andy5211d/SYMS17.0/pictures/IMG_2306.JPG

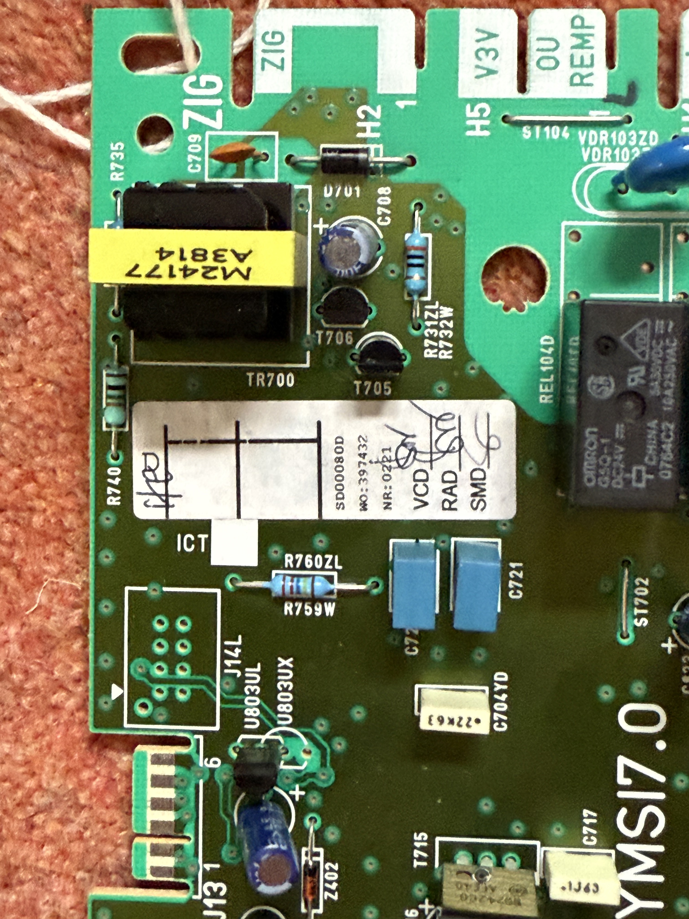
pictures/IMG_2306.JPG
