andy5211d/SYMS17.0/schematic/KiCad 8 Files/SYMS17.0.kicad_sch

## KiCad design schematic/KiCad 8 Files/SYMS17.0.kicad_sch (2025-01-01)

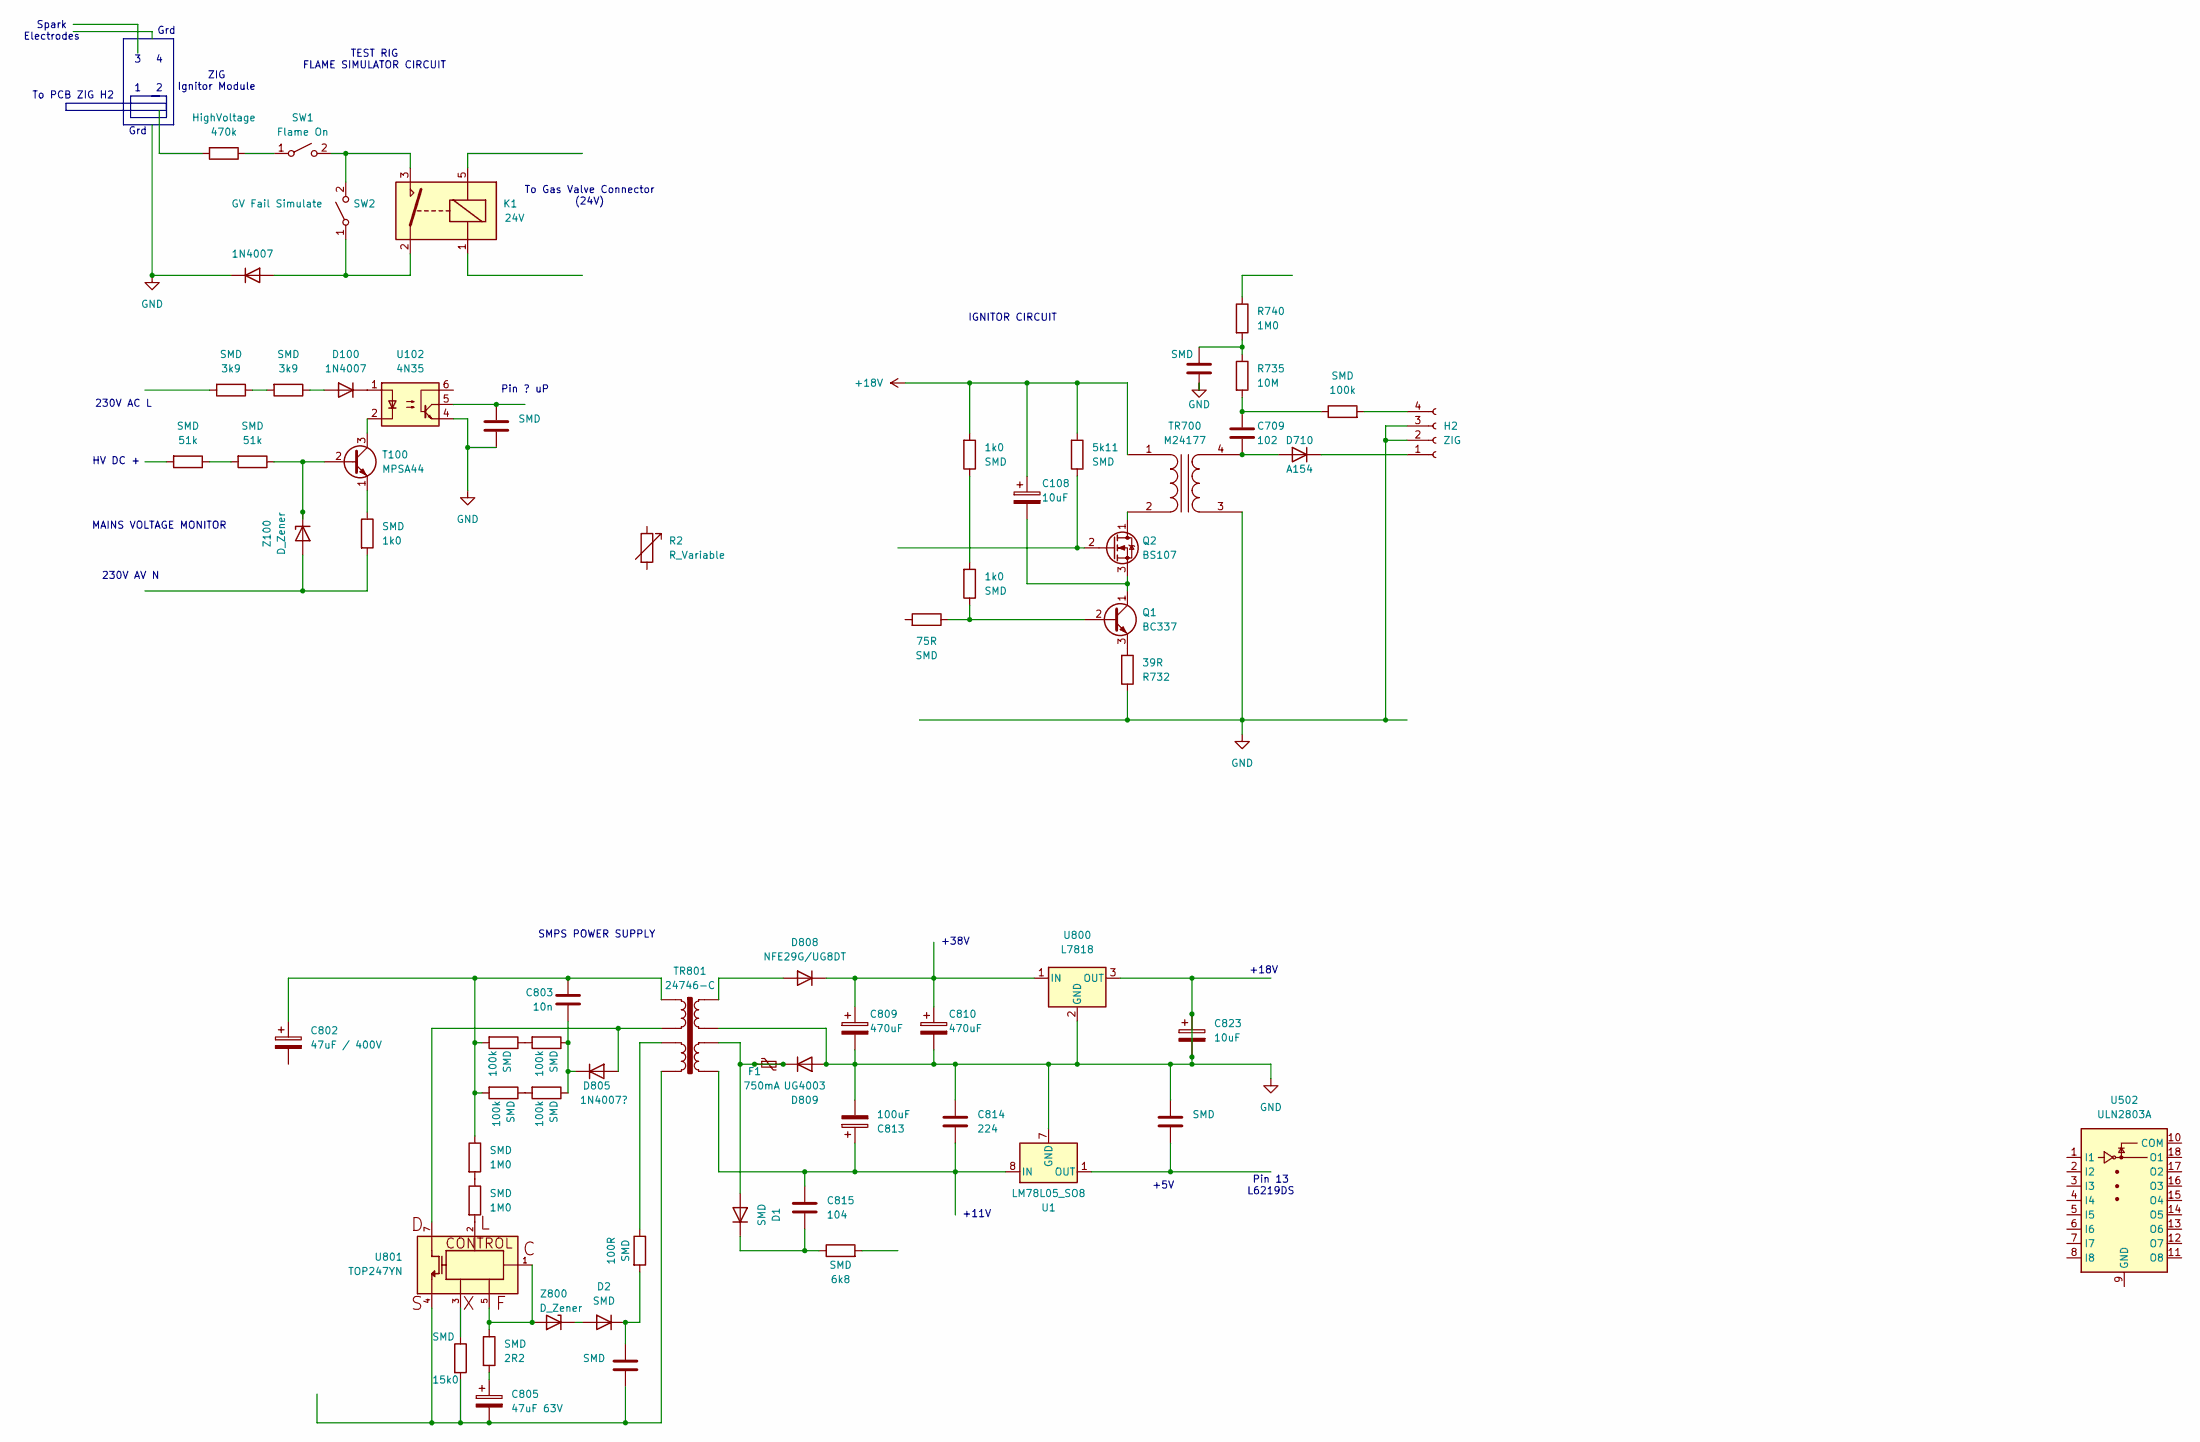
[picture p8: schematic SYMS17.0.kicad_sch]

Parts:
1N4007: (no value)
C108, C823: 10uF
C709: 102
C802: 47uF / 400V
C803: 10n
C805: 47uF 63V
C809, C810: 470uF
C813: 100uF
C814: 224
C815: 104
D1, D2: SMD; D_DO-201AD_P15.24mm_Horizontal
D100: 1N4007; D_DO-41_SOD81_P10.16mm_Horizontal
D710: A154
D805: 1N4007?; D_DO-201AD_P15.24mm_Horizontal
D808: NFE29G/UG8DT; D_DO-201AD_P15.24mm_Horizontal
D809: UG4003; D_DO-201AD_P15.24mm_Horizontal
F1: 750mA
HighVoltage: 470k
K1: 24V; Relay_SPST_Omron-G5Q-1A
Q1: BC337; TO-92_Inline
Q2: BS107; TO-92_Inline
R2: R_Variable
R732: 39R
R735: 10M
R740: 1M0
SMD: 51k
SW1: Flame On
SW2: GV Fail Simulate
T100: MPSA44; TO-92_Inline
TR700: M24177
TR801: 24746-C
U1: LM78L05_SO8; SOIC-8_3.9x4.9mm_P1.27mm
U102: 4N35; DIP-6_W7.62mm
U502: ULN2803A
U800: L7818
U801: TOP247YN; IC_TOP247YN; PARTREV 0
Z100, Z800: D_Zener
ZIG: H2

Connections:
+18V: C108.1, SMD.2, TR700.1 (AA)
GND: 1N4007.1 (K), C809.2, C810.2, C813.2, C814.1, C823.1, C823.2, D809.2 (A), R732.1, SMD.1, SMD.2, TR700.3 (SA), TR801.7, U1.2 (GND), U1.3 (GND), U1.6 (GND), U1.7 (GND), U102.4, U800.2 (GND), U800.3 (OUT), ZIG.2, ZIG.3
unnamed: 1N4007.2 (A), K1.2, SW2.1 (A)
unnamed: C108.2, Q1.1 (C), Q2.3 (S)
unnamed: C709.1, R735.2, SMD.1
unnamed: C709.2, D710.2 (A), TR700.4 (SB)
unnamed: C802.1, C803.1, SMD.1, SMD.2, TR801.1
unnamed: C803.2, D805.1 (K), SMD.1
unnamed: C805.1, SMD.2
unnamed: C805.2, SMD.2, TR801.4, U801.4
unnamed: C809.1, C810.1, D808.1 (K), U800.1 (IN)
unnamed: C813.1, C814.2, C815.1, TR801.5, U1.8 (IN)
unnamed: C815.2, D1.1 (K), SMD.1
unnamed: D1.2 (A), D809.1 (K), F1.1, F1.2, TR801.6
unnamed: D2.1 (K), SMD.1, SMD.2
unnamed: D2.2 (A), Z800.1 (K)
unnamed: D100.1 (K), U102.1
unnamed: D100.2 (A), SMD.1
unnamed: D710.1 (K), ZIG.1
unnamed: D805.2 (A), TR801.2, U801.7
unnamed: D808.2 (A), TR801.8
unnamed: HighVoltage.1, SW1.1 (A)
unnamed: K1.3, SW1.2 (B), SW2.2 (B)
unnamed: Q1.2 (B), SMD.1
unnamed: Q1.3 (E), R732.2
unnamed: Q2.1 (D), TR700.2 (AB)
unnamed: Q2.2 (G), SMD.1
unnamed: R735.1, R740.2, SMD.1
unnamed: SMD.1, SMD.2, T100.1 (E), T100.2 (B), TR801.3, U102.5, U801.1, U801.3, U801.5, Z100.1 (K), Z800.2 (A)
unnamed: SMD.2, U1.1 (OUT), U801.2, Z100.2 (A), ZIG.4
unnamed: T100.3 (C), U102.2

Notes on the sheet:
ZIG Ignitor Module
Grd
SMPS POWER SUPPLY
+5V
Pin 13 L6219DS
+38V
To PCB ZIG H2
230V AC L
Spark Electrodes
Pin ? uP
+11V
MAINS VOLTAGE MONITOR
To Gas Valve Connector (24V)
230V AV N
IGNITOR CIRCUIT
+18V
HV DC +
TEST RIG FLAME SIMULATOR CIRCUIT
